bablokb/circuitpython-vameter/src/FakeDataProvider.py

# ----------------------------------------------------------------------------
# FakeDataProvider.py: emulate data-provider (for tests)
#
# Author: Bernhard Bablok
# License: GPL3
#
# Website: https://github.com/bablokb/circuitpython-vameter
#
# ----------------------------------------------------------------------------

import time
import math

#DIM = 2
DIM = 3

class DataProvider:
  """ provide (fake) data """

  # --- constructor   --------------------------------------------------------

  def __init__(self,i2c,settings):
    """ constructor """

    self._settings = settings
    self.reset()

  # --- reset data-provider   ------------------------------------------------

  def reset(self):
    """ reset data-provider """
    self._start = None

  # --- return dimensions of data   ------------------------------------------

  def get_dim(self):
    """ dimension of data """
    return DIM

  # --- return units of data   -----------------------------------------------

  def get_units(self):
    """ units of data """
    if DIM == 2:
      return ['V','mA']
    else:
      return ['V','V','mA']

  # --- log-format   ---------------------------------------------------------

  def get_fmt(self):
    """ return format for data, timestamp is {0} """
    if DIM == 2:
      return "{1:.2f},{2:.1f}"
    else:
      return "{1:.2f},{2:.1f},{3:.1f}"

  # --- provide data   -------------------------------------------------------

  def get_data(self):
    """ yield the next measurement """

    time.sleep(0.01)
    t = time.monotonic()
    if not self._start:
      self._start = t
    if self._settings.duration == 0 and t > self._start + 60:
      raise StopIteration
    if DIM == 2:
      return (5+t/10+math.sin(t),25+t/10+math.cos(t))
    else:
      return (1+t/100+math.sin(t),5+t/10+math.sin(t),25+t/10+math.cos(t))
